GergelyTuri/tFC-rig/Software/lickport.h

// class for different lick ports
#ifndef LICKPORT_H
#define LICKPORT_H
#include <Arduino.h>

// code for "regular" lickport
class lickport
{
private:
    /* data */
public:
    lickport(/* args */);
    ~lickport();
};

lickport::lickport(/* args */)
{
}

lickport::~lickport()
{
}

// code for ESP32 lickport

#endif // LICKPORT_H
